msgre/postreh/schema/postreh.kicad_sch

## KiCad design schema/postreh.kicad_sch (2022-04-20)

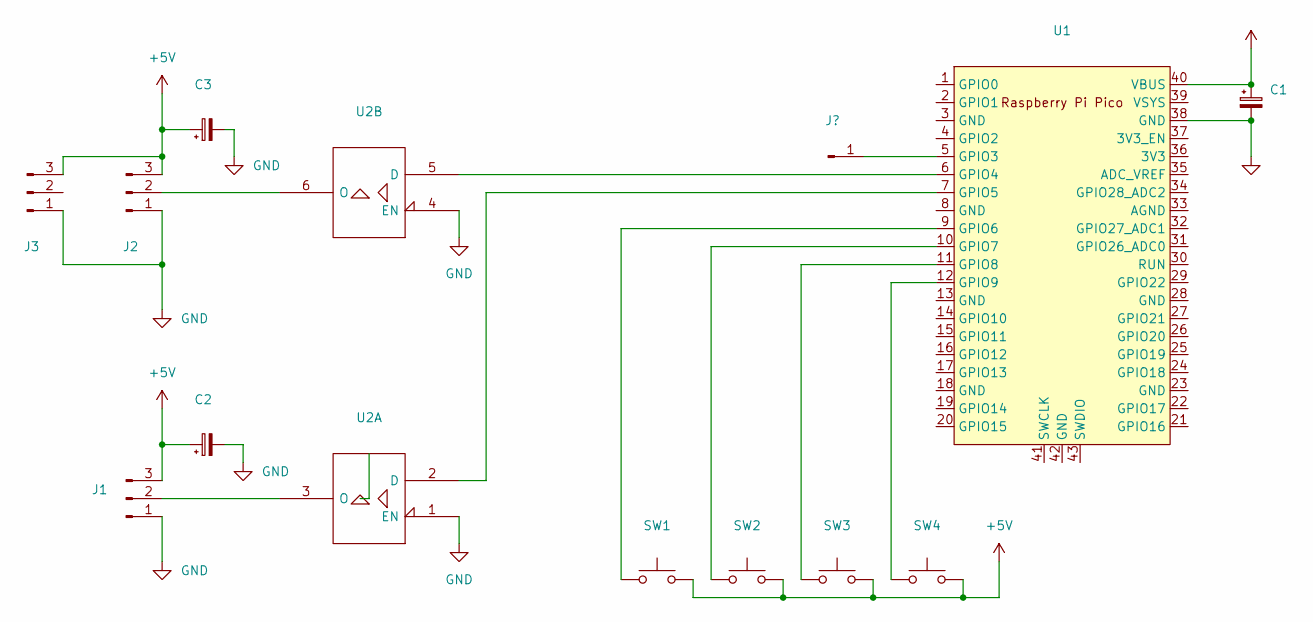
[picture p19: schematic postreh.kicad_sch]

Parts:
C1, C2, C3: (no value)
J1, J2, J3: (no value)
SW1, SW2, SW3, SW4: (no value)
U1, U2: (no value)

Connections:
unnamed: C1.1, U1.40 (VBUS)
unnamed: C1.2, U1.38 (GND)
unnamed: C2.1, J1.3
unnamed: C3.1, J2.3, J3.3
unnamed: J1.2, U2.3 (O)
unnamed: J2.1, J3.1
unnamed: J2.2, U2.6 (O)
unnamed: SW1.1, U1.9 (GPIO6)
unnamed: SW1.2, SW2.2, SW3.2, SW4.2
unnamed: SW2.1, U1.10 (GPIO7)
unnamed: SW3.1, U1.11 (GPIO8)
unnamed: SW4.1, U1.12 (GPIO9)
unnamed: U1.6 (GPIO4), U2.5 (D)
unnamed: U1.7 (GPIO5), U2.2 (D)
